jobitjoseph/Desktop-Weather-Station/Images/Desktop weather  station PCB layers750.png

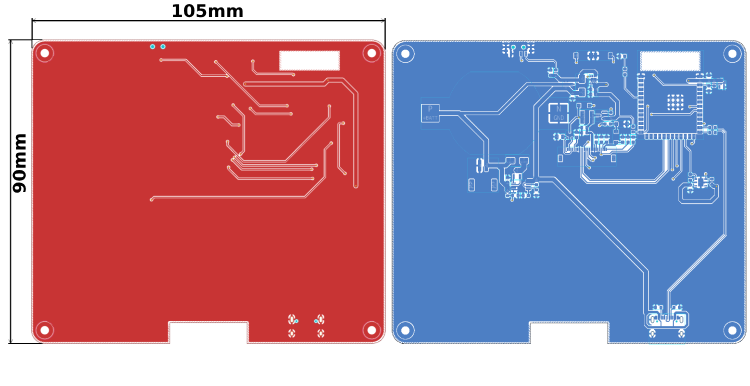
Images/Desktop weather station PCB layers750.png
