jobitjoseph/Desktop-Weather-Station/Images/Desktop Weather Station 3D back.png

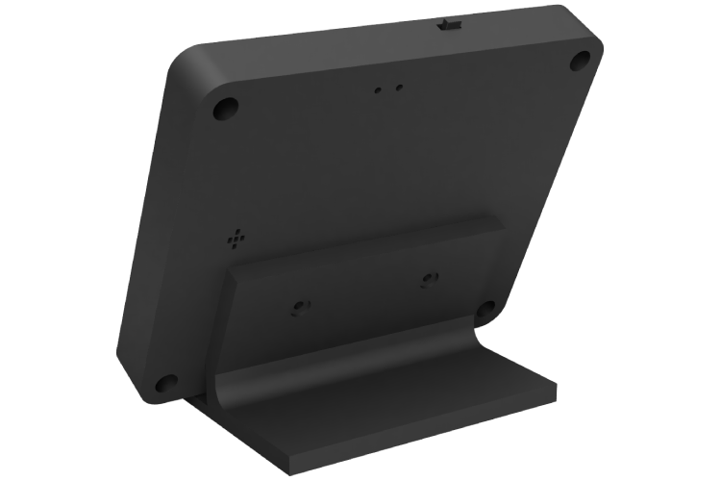
Images/Desktop Weather Station 3D back.png
