jobitjoseph/Desktop-Weather-Station/Images/Desktop Weather Station EPD Display Driver.png

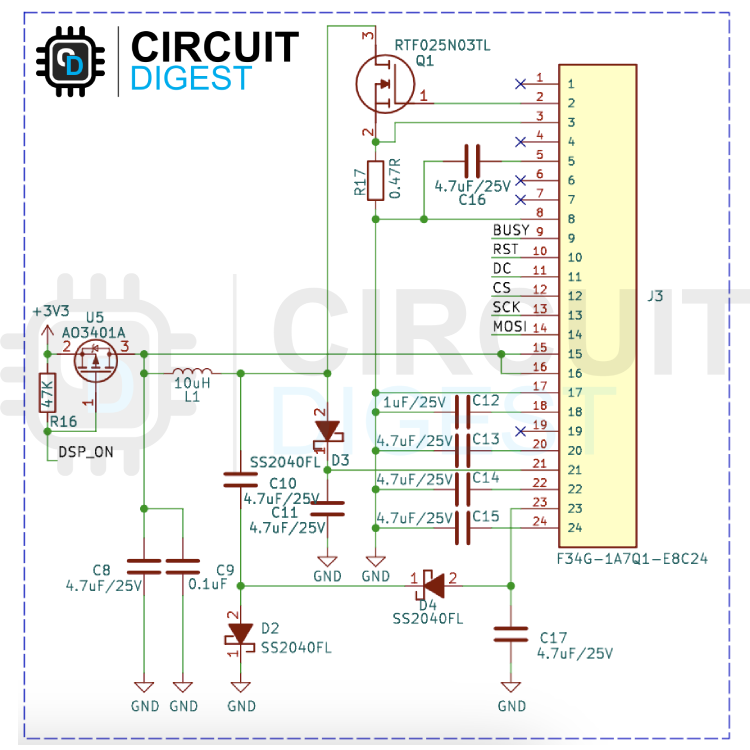
Images/Desktop Weather Station EPD Display Driver.png
