jobitjoseph/Desktop-Weather-Station/Images/Desktop Weather Station ESP32-S3 SoC.png

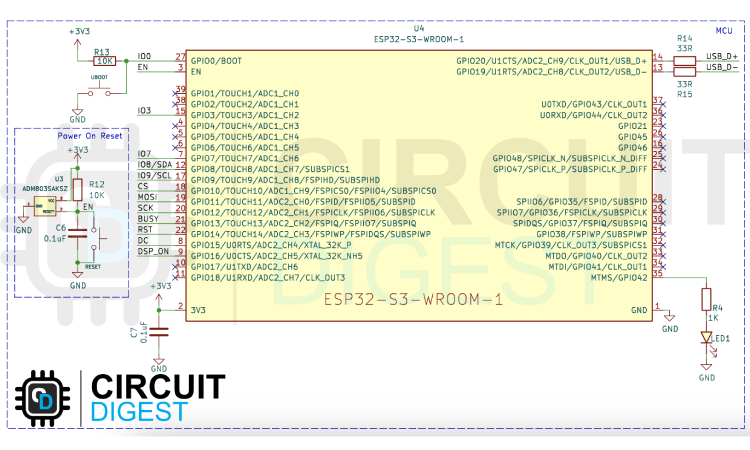
Images/Desktop Weather Station ESP32-S3 SoC.png
