jobitjoseph/Desktop-Weather-Station/Images/Desktop Weather Station Schematics 750.png

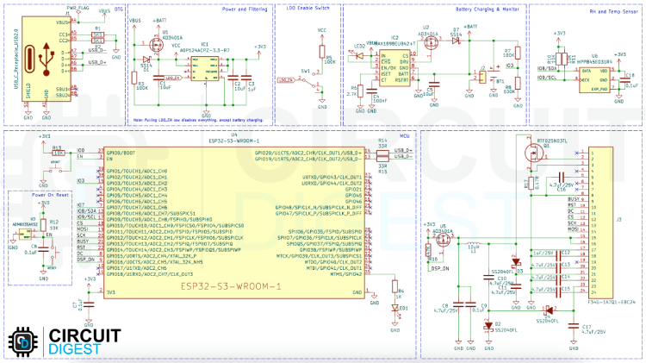
Images/Desktop Weather Station Schematics 750.png
