jobitjoseph/Desktop-Weather-Station/Images/Desktop Weather Station Temperature and Humidity Sensor (1).png

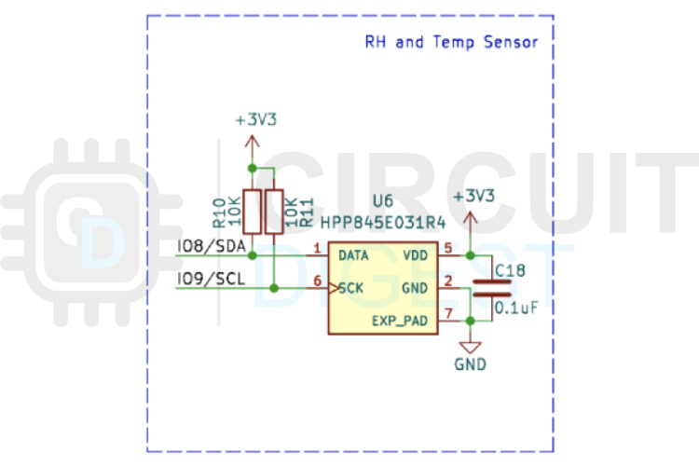
Images/Desktop Weather Station Temperature and Humidity Sensor (1).png
