jobitjoseph/Desktop-Weather-Station/Images/Desktop Weather Station Temperature and Humidity Sensor.png

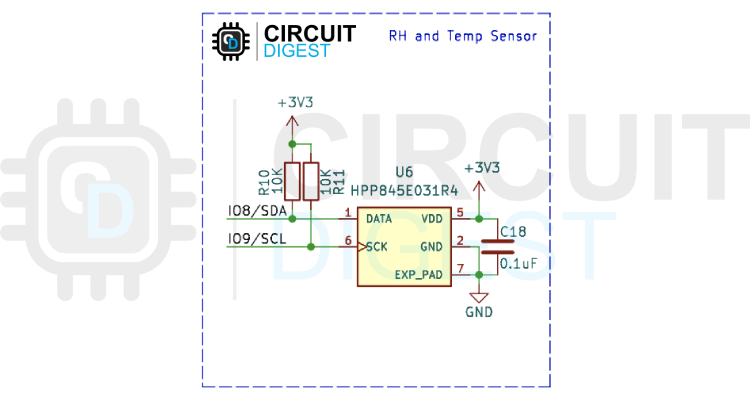
Images/Desktop Weather Station Temperature and Humidity Sensor.png
