jobitjoseph/Desktop-Weather-Station/PCB/Low Power Desktop Weather Station/Low Power Desktop Weather Station Back.png

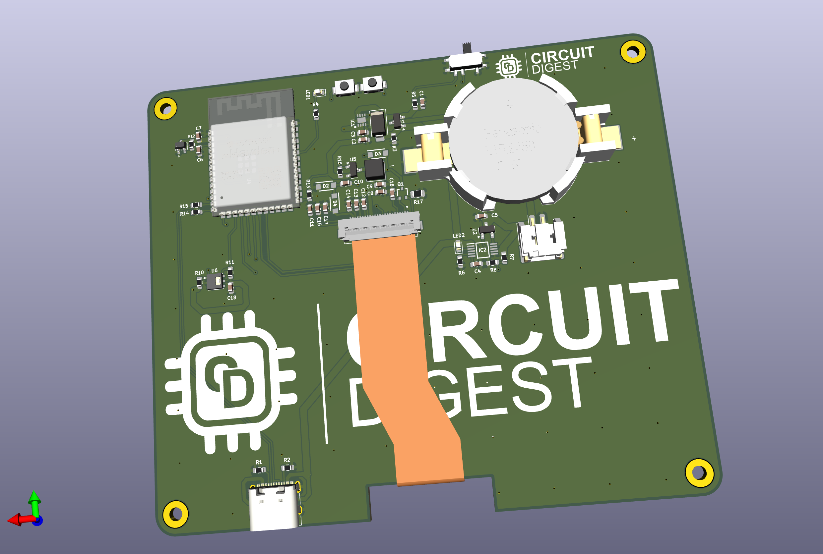
PCB/Low Power Desktop Weather Station/Low Power Desktop Weather Station Back.png
