jobitjoseph/Desktop-Weather-Station/PCB/Low Power Desktop Weather Station/Low Power Desktop Weather Station.png

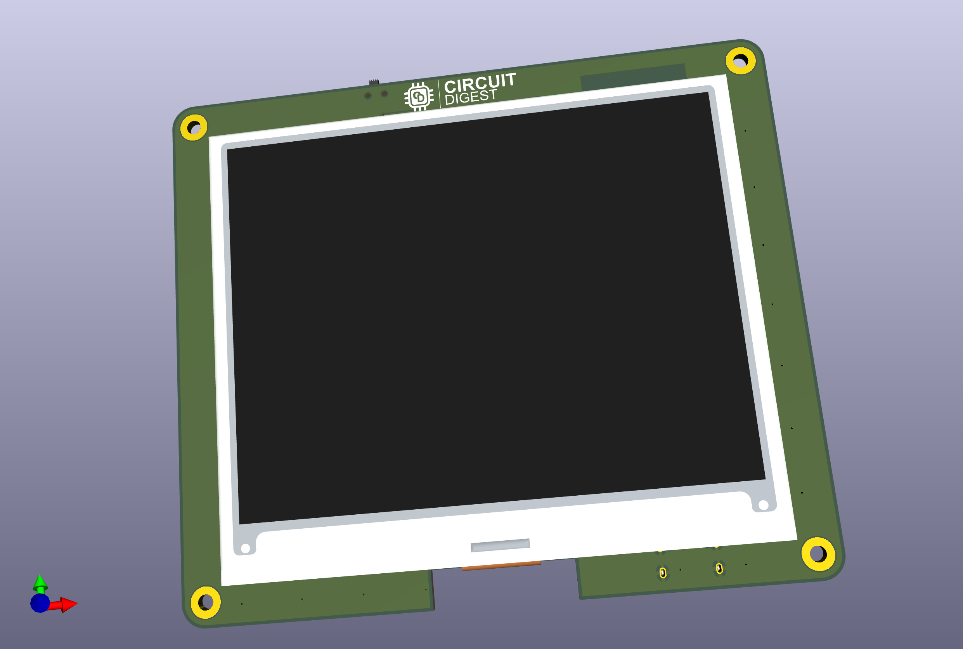
PCB/Low Power Desktop Weather Station/Low Power Desktop Weather Station.png
