jobitjoseph/Desktop-Weather-Station/Images/Desktop Weather Station 3D Parts.png

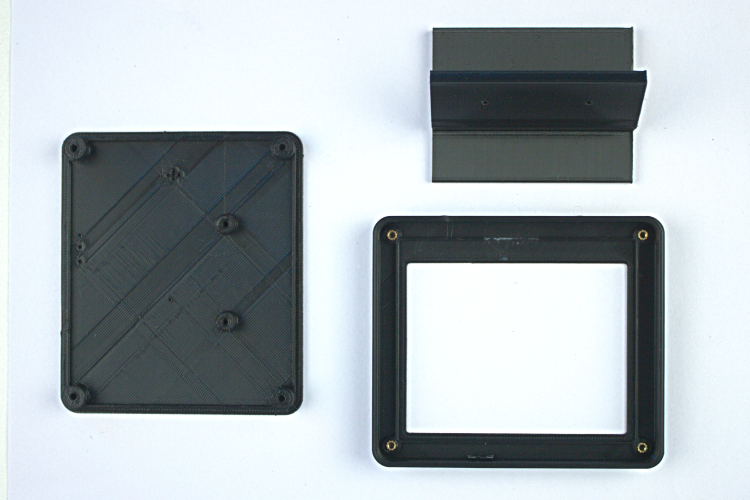
Images/Desktop Weather Station 3D Parts.png
